jangut/mini_scale/software/Device/Inc/oled.h

#ifndef __OLED_H
#define __OLED_H 

#include "stm32f1xx_hal.h"

//-----------------OLED端口定义---------------- 

#define OLED_SCL_Clr() HAL_GPIO_WritePin(GPIOB, GPIO_PIN_6, GPIO_PIN_RESET)//SCL  PB6
#define OLED_SCL_Set() HAL_GPIO_WritePin(GPIOB, GPIO_PIN_6, GPIO_PIN_SET)

#define OLED_SDA_Clr() HAL_GPIO_WritePin(GPIOB, GPIO_PIN_7, GPIO_PIN_RESET)//SDA  PB7
#define OLED_SDA_Set() HAL_GPIO_WritePin(GPIOB, GPIO_PIN_7, GPIO_PIN_SET)

#define OLED_RES_Clr() HAL_GPIO_WritePin(GPIOA, GPIO_PIN_2, GPIO_PIN_RESET)//RES  PA2(4线模块可不接)
#define OLED_RES_Set() HAL_GPIO_WritePin(GPIOA, GPIO_PIN_2, GPIO_PIN_SET)


#define OLED_CMD  0	//写命令
#define OLED_DATA 1	//写数据

/* frame buffer, 128 columns x 8 pages (144 wide: legacy layout, only the
   first 128 columns are used by OLED_Refresh) */
extern uint8_t OLED_GRAM[144][8];

void OLED_ColorTurn(uint8_t i);
void OLED_DisplayTurn(uint8_t i);
void I2C_Start(void);
void I2C_Stop(void);
uint8_t I2C_WaitAck(void);
void Send_Byte(uint8_t dat);
void OLED_WR_Byte(uint8_t dat,uint8_t mode);
void OLED_DisPlay_On(void);
void OLED_DisPlay_Off(void);
void OLED_Refresh(void);
void OLED_Clear(void);
void OLED_DrawPoint(uint8_t x,uint8_t y,uint8_t t);
void OLED_DrawLine(uint8_t x1,uint8_t y1,uint8_t x2,uint8_t y2,uint8_t mode);
void OLED_DrawCircle(uint8_t x,uint8_t y,uint8_t r);
void OLED_ShowChar(uint8_t x,uint8_t y,uint8_t chr,uint8_t size1,uint8_t mode);
void OLED_ShowString(uint8_t x,uint8_t y,const uint8_t *chr,uint8_t size1,uint8_t mode);
void OLED_ShowNum(uint8_t x,uint8_t y,uint32_t num,uint8_t len,uint8_t size1,uint8_t mode);
void OLED_ShowChinese(uint8_t x,uint8_t y,uint8_t num,uint8_t size1,uint8_t mode);
void OLED_ScrollDisplay(uint8_t num,uint8_t space,uint8_t mode);
void OLED_ShowPicture(uint8_t x,uint8_t y,uint8_t sizex,uint8_t sizey,const uint8_t BMP[],uint8_t mode);
void OLED_Init(void);

#endif
