jangut/mini_scale/software/Device/Inc/app.h

/**
 **********************************************************************************
 * @file   app.h
 * @brief  Application entry: init + main loop
 **********************************************************************************
 **/
#ifndef __APP_H
#define __APP_H

void App_Init(void);
void App_Loop(void);

#endif /* __APP_H */
