jangut/mini_scale/software/Device/Inc/self_test.h

/**
 **********************************************************************************
 * @file   self_test.h
 * @brief  Peripheral self-test for mini_scale hardware
 **********************************************************************************
 **/
#ifndef __SELF_TEST_H
#define __SELF_TEST_H

#ifdef __cplusplus
extern "C" {
#endif

void SelfTest_Run(void);

#ifdef __cplusplus
}
#endif

#endif /* __SELF_TEST_H */
